retango/korg-ms20m-extra-midi2cv/hardware/Schematic.kicad_sch

## KiCad design hardware/Schematic.kicad_sch (2023-08-03)

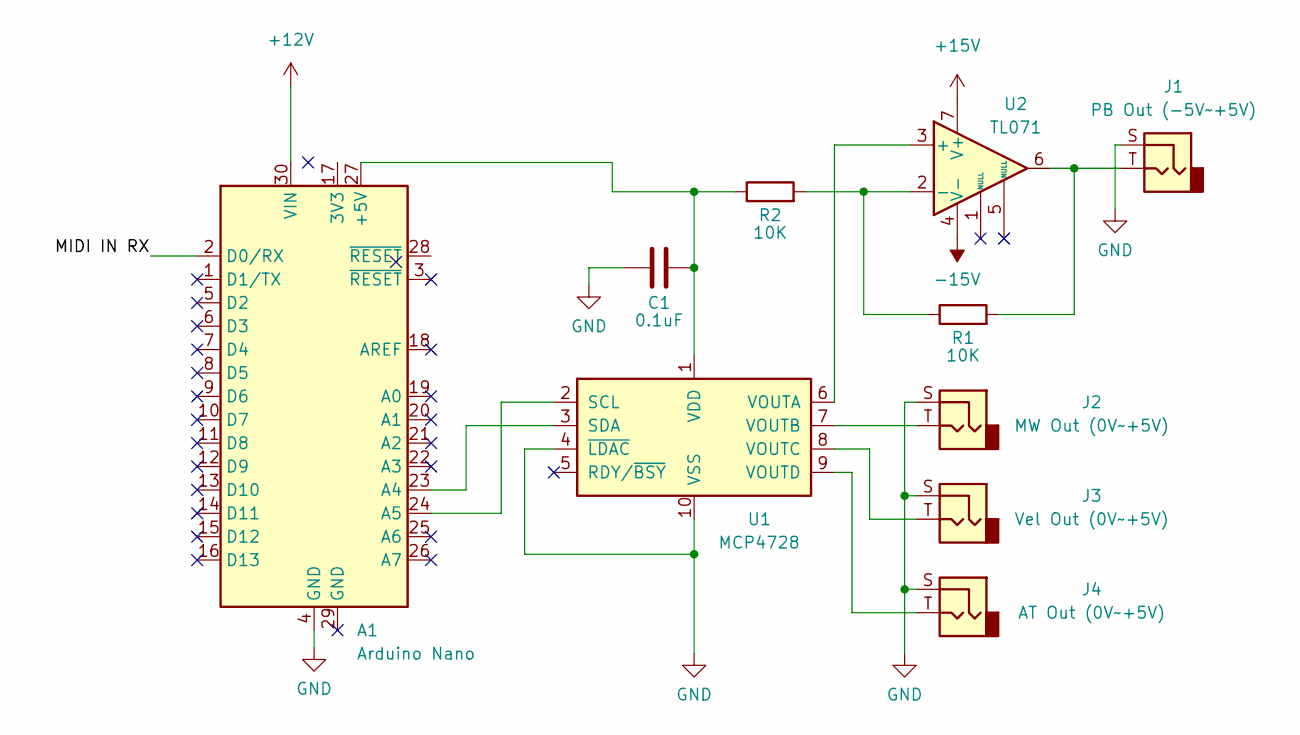
[picture p13: schematic Schematic.kicad_sch]

Parts:
A1: Arduino Nano; Arduino_Nano
C1: 0.1uF
J1: PB Out (-5V~+5V)
J2: MW Out (0V~+5V)
J3: Vel Out (0V~+5V)
J4: AT Out (0V~+5V)
R1, R2: 10K
U1: MCP4728; MSOP-10_3x3mm_P0.5mm
U2: TL071

Connections:
MIDI IN RX: A1.2 (D0/RX)
unnamed: A1.23 (A4), U1.3 (SDA)
unnamed: A1.24 (A5), U1.2 (SCL)
unnamed: A1.27 (+5V), C1.2, R2.1, U1.1 (VDD)
unnamed: J1.T, R1.2, U2.6
unnamed: J2.S, J3.S, J4.S
unnamed: J2.T, U1.7 (VOUTB)
unnamed: J3.T, U1.8 (VOUTC)
unnamed: J4.T, U1.9 (VOUTD)
unnamed: R1.1, R2.2, U2.2 (-)
unnamed: U1.6 (VOUTA), U2.3 (+)
unnamed: U1.4 (~LDAC), U1.10 (VSS)
